cyberboy666/r_e_c_u_r/user_input/numpad_input.py

import string
import sys

class NumpadInput(object):
    def __init__(self, root, message_handler, display, actions, data):
        self.root = root
        self.message_handler = message_handler
        self.display = display
        self.actions = actions
        self.data = data
        self.key_mappings = data.key_mappings
        self.bind_actions()
        self.in_0_event = False
        self.additional_0_in_event = 0

    def bind_actions(self):
        self.display.display_text.bind("<KeyPress>", self.on_key_press)
        self.display.display_text.bind("<KeyRelease>", self.on_key_release)

    def on_key_press(self, event):
        numpad = list(string.ascii_lowercase[0:19])

        if event.char is '.' or event.char is 'z':
            self.actions.quit_the_program()
        if event.char is 's':
            event.char = self.on_0_key_press()
        elif event.char in numpad:
            self.run_action_for_mapped_key(event.char)
        else:
            print('{} is not in keypad map'.format(event.char))

    def on_key_release(self, event):
            numpad = list(string.ascii_lowercase[0:19])
            if event.char in numpad:
                self.check_key_release_settings(event.char)

    def run_action_for_mapped_key(self, key):
        this_mapping = self.key_mappings[key]
        if self.data.control_mode in this_mapping:
            mode = self.data.control_mode
        elif 'DEFAULT' in this_mapping:
            mode = 'DEFAULT'

        if self.data.function_on and len(this_mapping[mode]) > 1:
            print('the action being called is {}'.format(this_mapping[mode][1]))
            getattr(self.actions, this_mapping[mode][1])()
            if self.data.settings['sampler']['FUNC_GATED']['value'] == 'off':
                self.data.function_on = False
        else:
            print('the action being called is {}'.format(this_mapping[mode][0]))
            getattr(self.actions, this_mapping[mode][0])()
      
        self.display.refresh_display()



    def check_key_release_settings(self, key):
        
        this_mapping = self.key_mappings[key]
        if self.data.settings['sampler']['ACTION_GATED']['value'] == 'on':
            if self.data.control_mode == 'PLAYER' and 'PLAYER' in this_mapping:
                if this_mapping['PLAYER'][0] == 'toggle_action_on_player' and not self.data.function_on:
                    print('released action key')
                    self.run_action_for_mapped_key(key)
        if self.data.settings['sampler']['FUNC_GATED']['value'] == 'on':
            if 'DEFAULT' in this_mapping:
                if this_mapping['DEFAULT'][0] == 'toggle_function':
                    self.run_action_for_mapped_key(key)
        

    def on_0_key_press(self) :
        if(not self.in_0_event ):
            self.in_0_event  = True
            self.additional_0_in_event = 0
            self.root.after(600, self.check_event_outcome)
        else:
            self.additional_0_in_event = self.additional_0_in_event + 1 

    def check_event_outcome(self):
        if(self.additional_0_in_event == 0 ):
            self.in_0_event  = False
            self.run_action_for_mapped_key('s')
        elif(self.additional_0_in_event > 1):
            self.in_0_event  = False
            self.run_action_for_mapped_key('n')
        elif(self.additional_0_in_event == 1):
            print('this doesnt happen - may not be needed')
            self.root.after(600, self.second_check_event_outcome)

    def second_check_event_outcome(self):
        if(self.additional_0_in_event == 1 ):
            self.in_0_event  = False
            self.run_action_for_mapped_key('s')
        elif(self.additional_0_in_event > 1):
            self.in_0_event  = False
            self.run_action_for_mapped_key('n')
